lwollinger/Projeto-Brinquedo-M-gico/implement/drills_3d_simulacoes/3d/9v Battery Holder - 2144462/images/799430a5e998552866c055b1087d3175.png

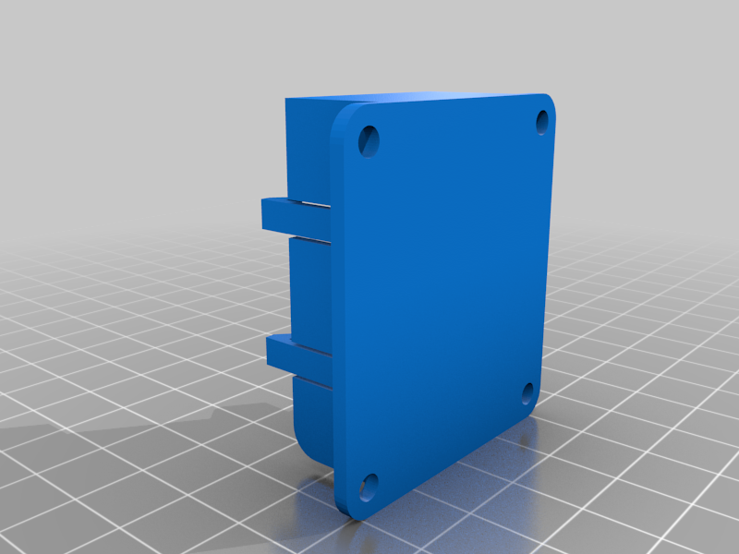
implement/drills_3d_simulacoes/3d/9v Battery Holder - 2144462/images/799430a5e998552866c055b1087d3175.png
