lwollinger/Projeto-Brinquedo-M-gico/implement/drills_3d_simulacoes/3d/9v Battery Holder - 2144462/images/Battery_holder.jpg

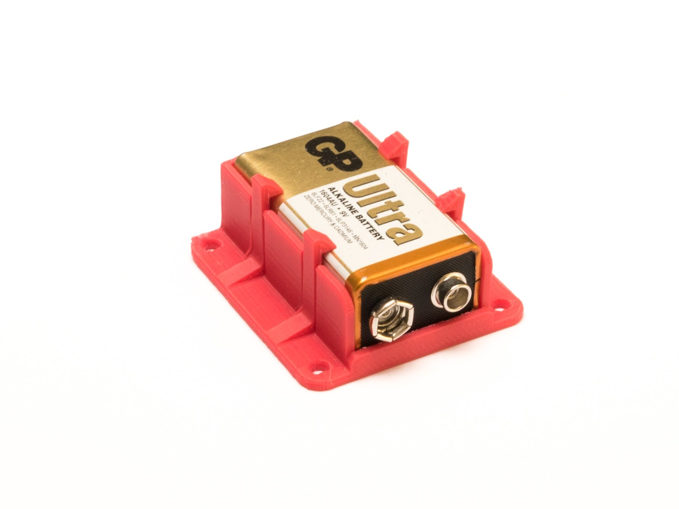
implement/drills_3d_simulacoes/3d/9v Battery Holder - 2144462/images/Battery_holder.jpg
